a-trillet/STIB-display/cpp/bus_display_led/main/led_controller.h

// led_controller.h
#pragma once

#include "driver/gpio.h"
#include "esp_log.h"
#include <cstdint>


// GPIO Pin Definitions
#define CLOCK_PIN GPIO_NUM_18
#define DATA_PIN GPIO_NUM_15
#define LATCH_PIN GPIO_NUM_5
#define RESET_PIN GPIO_NUM_19
#define OE_PIN GPIO_NUM_2

// Timing
#define PULSE_DELAY_US 200

class LEDController {
public:
    LEDController();
    ~LEDController();
    
    bool initialize();
    void set_leds(uint16_t pattern);
    void set_single_led(int led_number);
    void clear_all();
    void set_all(const bool state);
    void test_sequence();
    void set_rows(const bool rows[][12], size_t row_count);
    
private:
    void pulse_pin(gpio_num_t pin);
    void feed_register(uint16_t value);
    void latch_data();
    bool initialized_;
    
    static const char* TAG;
    
    // LED to register bit mapping (from your original code)
    static const uint16_t led_to_register[12];
};
